nachdenksport/openlift/STL/Reduzierringe/v1.2/30mm - Reduzierring v1.2.stl

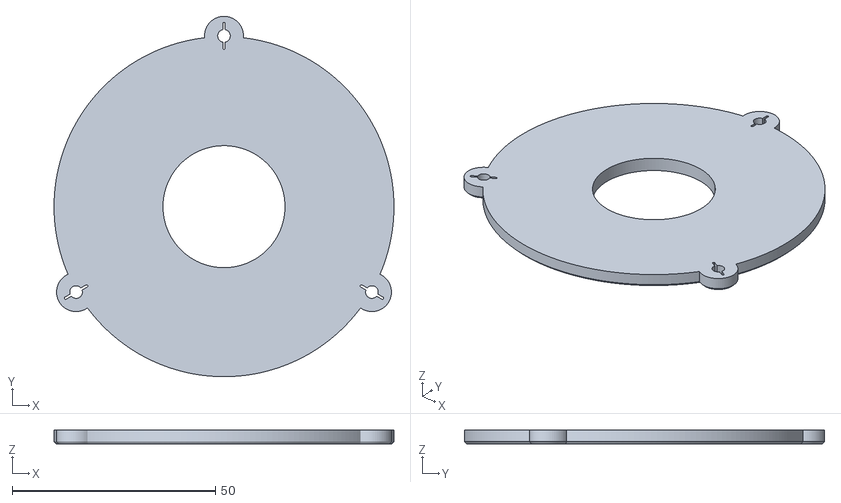
[picture p16: CAD file, 2023-05-16, an earlier design]
STL/Reduzierringe/v1.2/30mm - Reduzierring v1.2.stl
83.6 x 88.6 x 3.45
