nachdenksport/openlift/STL/Fraeslift/v1.3/Handkurbel.stl

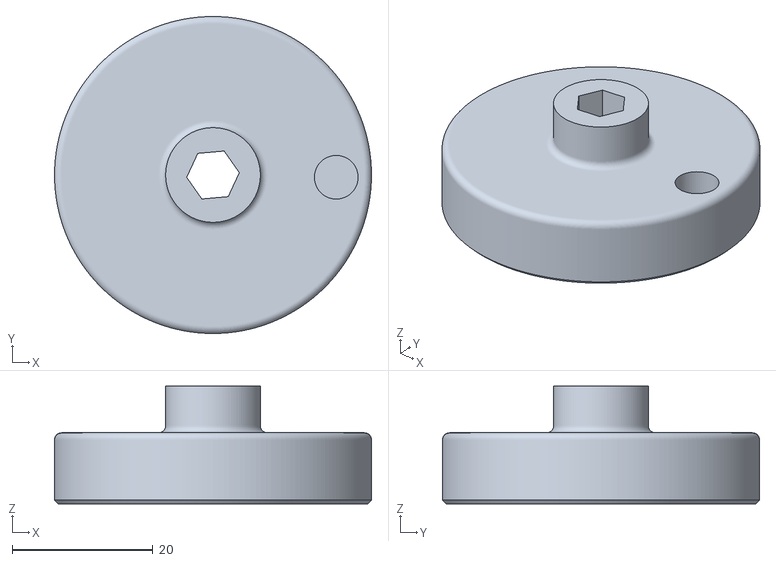
[picture p17: CAD file, 2022-04-29, an earlier design]
STL/Fraeslift/v1.3/Handkurbel.stl
45.0 x 45.0 x 16.7
